ReSummit/Seismos/3dmodels/case/Plate/Plate_Rails.3mf

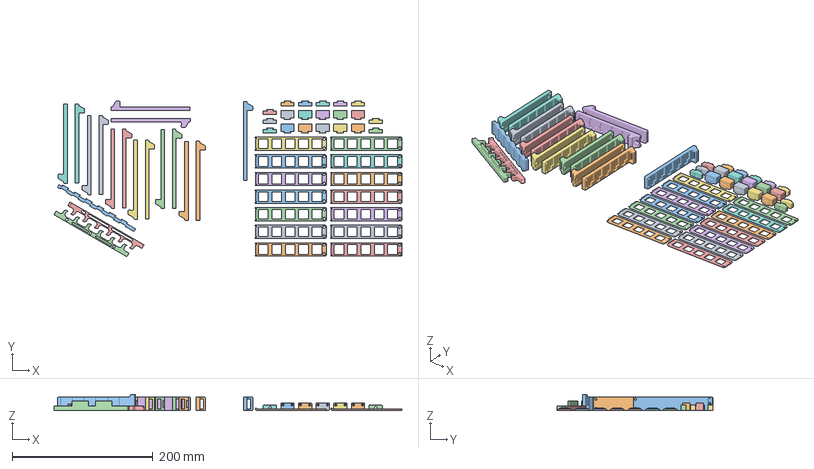
[picture p18: CAD file, 2023-12-05]
3dmodels/case/Plate/Plate_Rails.3mf
493.9 x 220.8 x 22.8 mm
Plate - Part 4.stl
Plate - Part 2.stl
Plate - Part 3.stl
Plate - Part 1.stl
Plate Optimal
Mantle - Part 2.stl
Mantle - Part 3.stl
Mantle - Part 4.stl
