ReSummit/Seismos/3dmodels/case/Plate/Plate - Part 2.stl

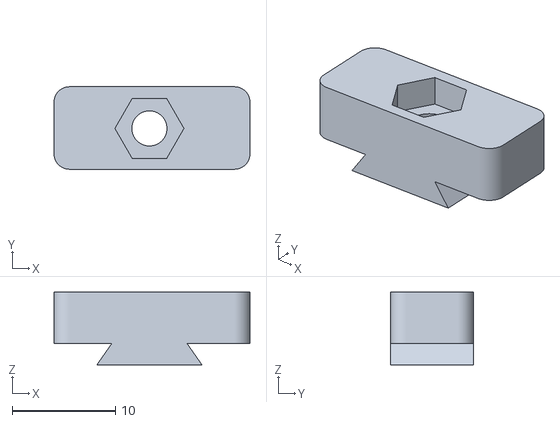
[picture p19: CAD file, 2023-12-05]
3dmodels/case/Plate/Plate - Part 2.stl
19.0 x 8.00 x 7.05
