ReSummit/Seismos/pcbs/Deprecated PCBs (DO NOT USE)/(OLD) Seismos_CoreStencil/(OLD) Seismos_CoreStencil.kicad_pcb

## KiCad design pcbs/Deprecated PCBs (DO NOT USE)/(OLD) Seismos_CoreStencil/(OLD) Seismos_CoreStencil.kicad_pcb (2023-11-11, an earlier design)

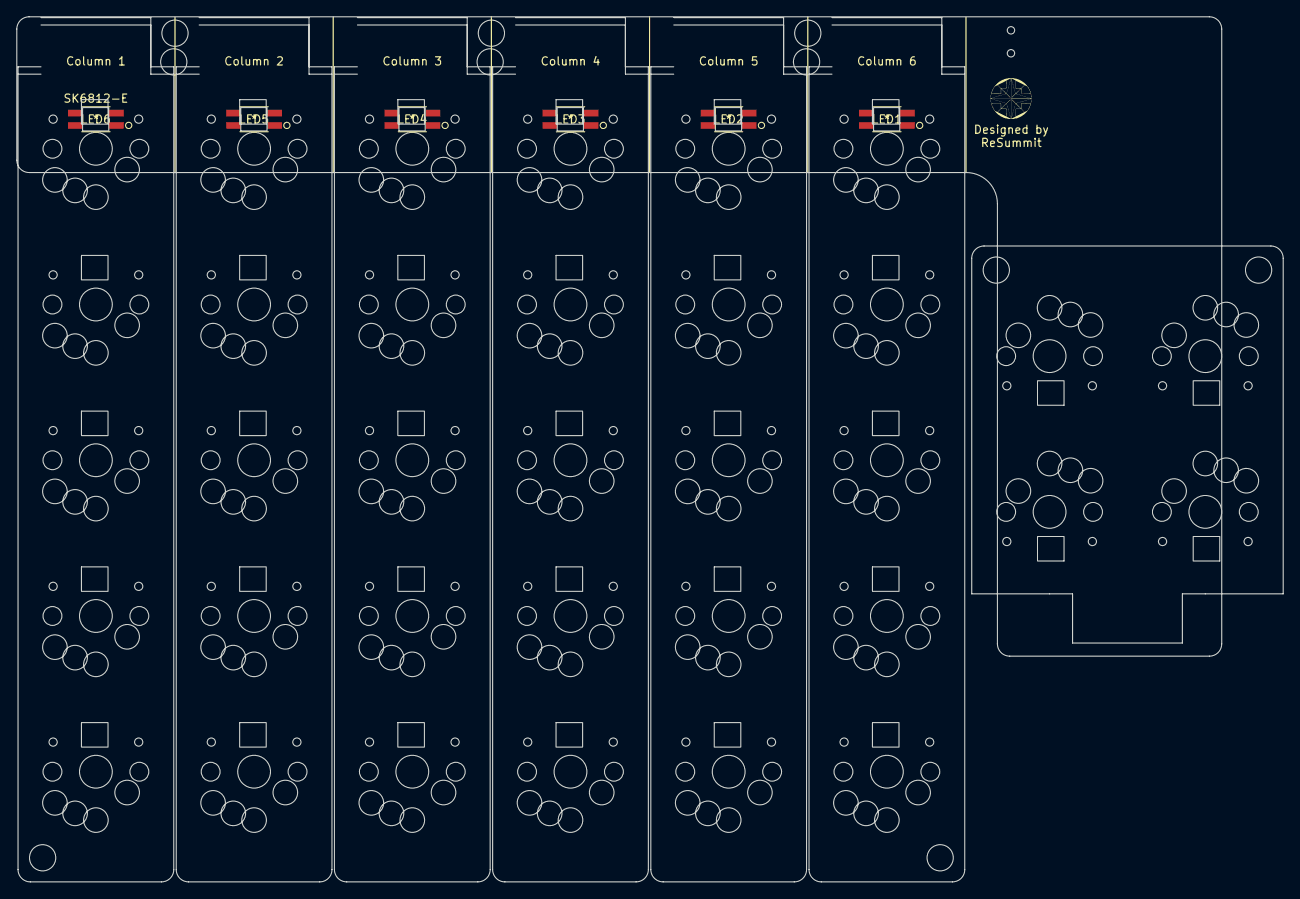
[picture p31: board (OLD) Seismos_CoreStencil.kicad_pcb from above]

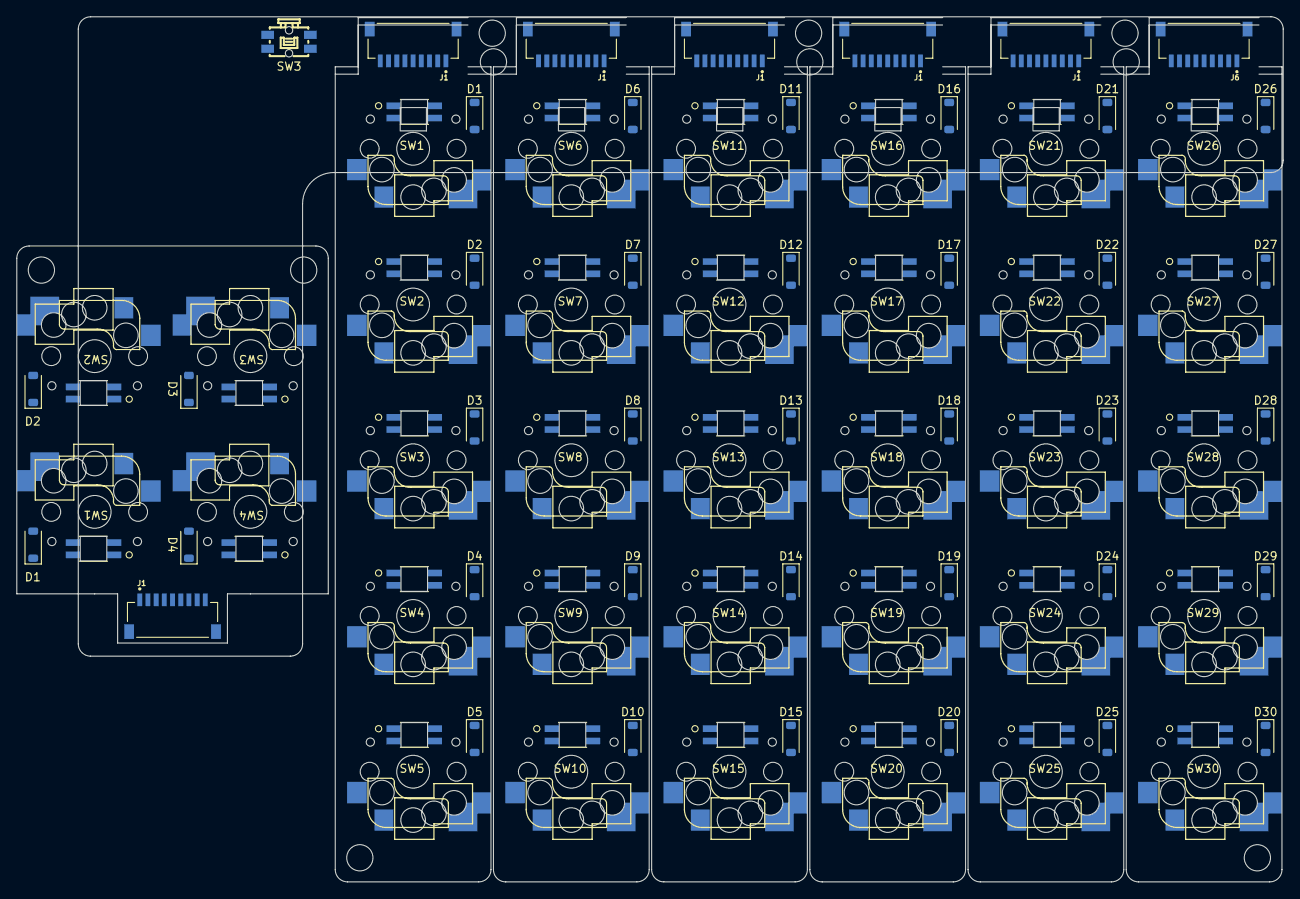
[picture p32: board (OLD) Seismos_CoreStencil.kicad_pcb from below]

Board: 2 copper layers, 154.5 x 105.5 mm, 83 parts (82 on the bottom side), 10 nets, no tracks yet.

Parts:
4: Hole_M3_3.2mm
D1, D1#2, D2, D2#2, D3, D3#2, D4, D4#2, D5, D6, D7, D8, D9, D10, D11, D12, D13, D14, D15, D16, D17, D18, D19, D20, D21, D22, D23, D24, D25, D26, D27, D28, D29, D30: 1N4148W; D_SOD-123
J1, J1#2, J1#3, J1#4, J1#5, J1#6, J6: SM09B-SRSS-TB(LF)(SN); JST_SM09B-SRSS-TB(LF)(SN)
LED1, LED2, LED3, LED4, LED5, LED6: SK6812-E
SW1, SW1#2, SW2, SW2#2, SW3, SW3#3, SW4, SW4#2, SW5, SW6, SW7, SW8, SW9, SW10, SW11, SW12, SW13, SW14, SW15, SW16, SW17, SW18, SW19, SW20, SW21, SW22, SW23, SW24, SW25, SW26, SW27, SW28, SW29, SW30: Switch_SK6812-E_Diode
SW3#2: EVQPUC02K; SW-SMD_EVQPUD02K

Connections:
/RGB_In6: J6.6, LED5.2 (DOUT)
/RGB_Out6: J6.9, LED6.4 (DIN)
/Row1: D1.1 (K), D1#2.1 (K), D6.1 (K), D11.1 (K), D16.1 (K), D21.1 (K), D26.1 (K), J6.2
/Row2: D2.1 (K), D2#2.1 (K), D7.1 (K), D12.1 (K), D17.1 (K), D22.1 (K), D27.1 (K), J6.3
/Row3: D3.1 (K), D3#2.1 (K), D8.1 (K), D13.1 (K), D18.1 (K), D23.1 (K), D28.1 (K), J6.4
/Row4: D4.1 (K), D4#2.1 (K), D9.1 (K), D14.1 (K), D19.1 (K), D24.1 (K), D29.1 (K), J6.5
/Row5: D5.1 (K), D10.1 (K), D15.1 (K), D20.1 (K), D25.1 (K), D30.1 (K)
/V+: J6.8, LED1.1 (VDD), LED2.1 (VDD), LED3.1 (VDD), LED4.1 (VDD), LED5.1 (VDD), LED6.1 (VDD), SW1.+1 (VDD), SW1#2.+1 (VDD), SW2.+1 (VDD), SW2#2.+1 (VDD), SW3.+1 (VDD), SW3#3.+1 (VDD), SW4.+1 (VDD), SW4#2.+1 (VDD), SW5.+1 (VDD), SW6.+1 (VDD), SW7.+1 (VDD), SW8.+1 (VDD), SW9.+1 (VDD), SW10.+1 (VDD), SW11.+1 (VDD), SW12.+1 (VDD), SW13.+1 (VDD), SW14.+1 (VDD), SW15.+1 (VDD), SW16.+1 (VDD), SW17.+1 (VDD), SW18.+1 (VDD), SW19.+1 (VDD), SW20.+1 (VDD), SW21.+1 (VDD), SW22.+1 (VDD), SW23.+1 (VDD), SW24.+1 (VDD), SW25.+1 (VDD), SW26.+1 (VDD), SW27.+1 (VDD), SW28.+1 (VDD), SW29.+1 (VDD), SW30.+1 (VDD)
GND: J6.1, J6.S1 (SHIELD), J6.S2 (SHIELD), LED1.3 (GND), LED2.3 (GND), LED3.3 (GND), LED4.3 (GND), LED5.3 (GND), LED6.3 (GND), SW1.GND, SW1#2.GND, SW2.GND, SW2#2.GND, SW3.GND, SW3#2.2, SW3#2.4, SW3#3.GND, SW4.GND, SW4#2.GND, SW6.GND, SW7.GND, SW8.GND, SW9.GND, SW11.GND, SW12.GND, SW13.GND, SW14.GND, SW16.GND, SW17.GND, SW18.GND, SW19.GND, SW21.GND, SW22.GND, SW23.GND, SW24.GND, SW26.GND, SW27.GND, SW28.GND, SW29.GND
RESET: SW3#2.1, SW3#2.3
